madeinchaos/eins2440/hardware/images/1.jpg

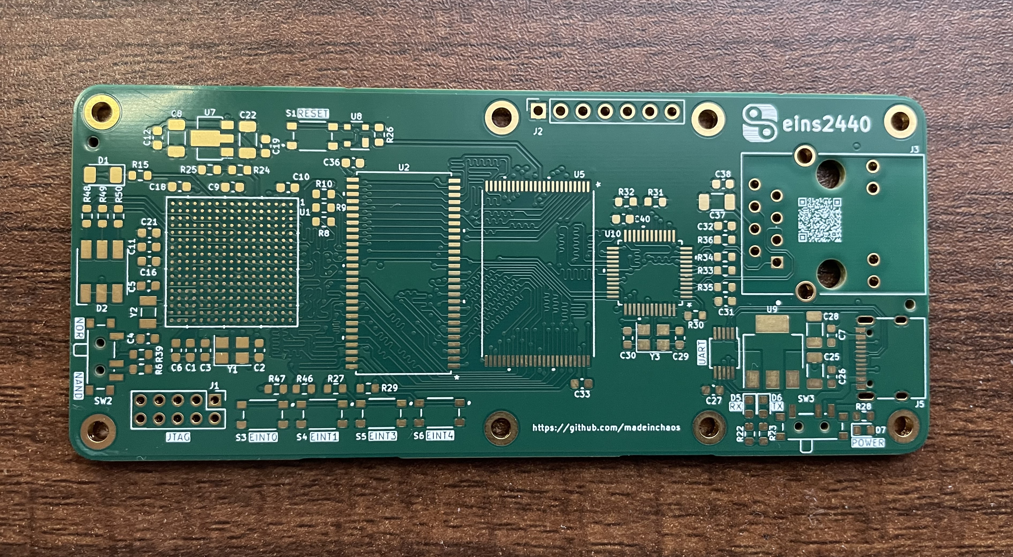
hardware/images/1.jpg
