madeinchaos/eins2440/hardware/images/2.jpg

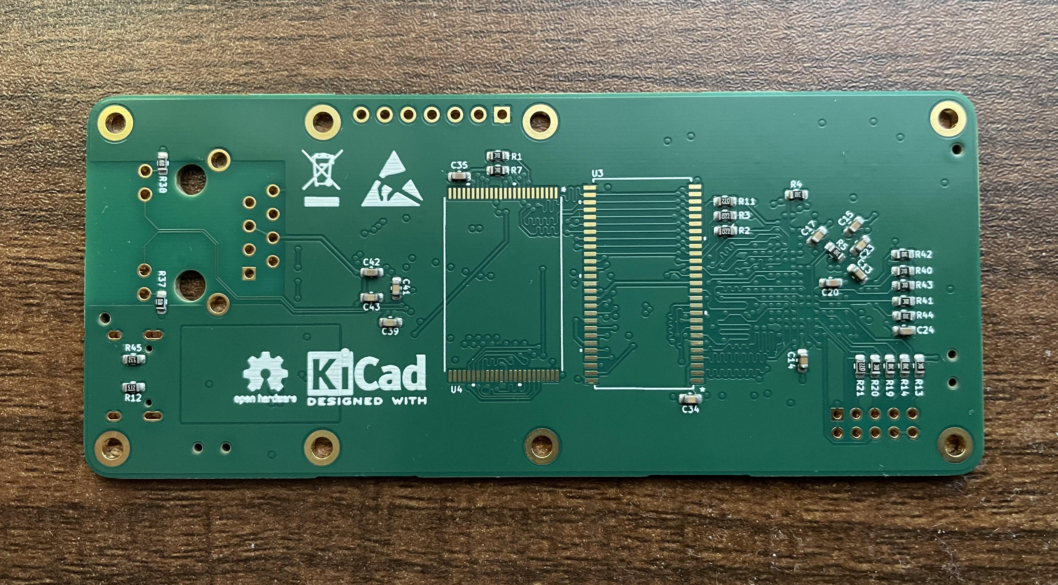
hardware/images/2.jpg
