madeinchaos/eins2440/hardware/images/3.jpg

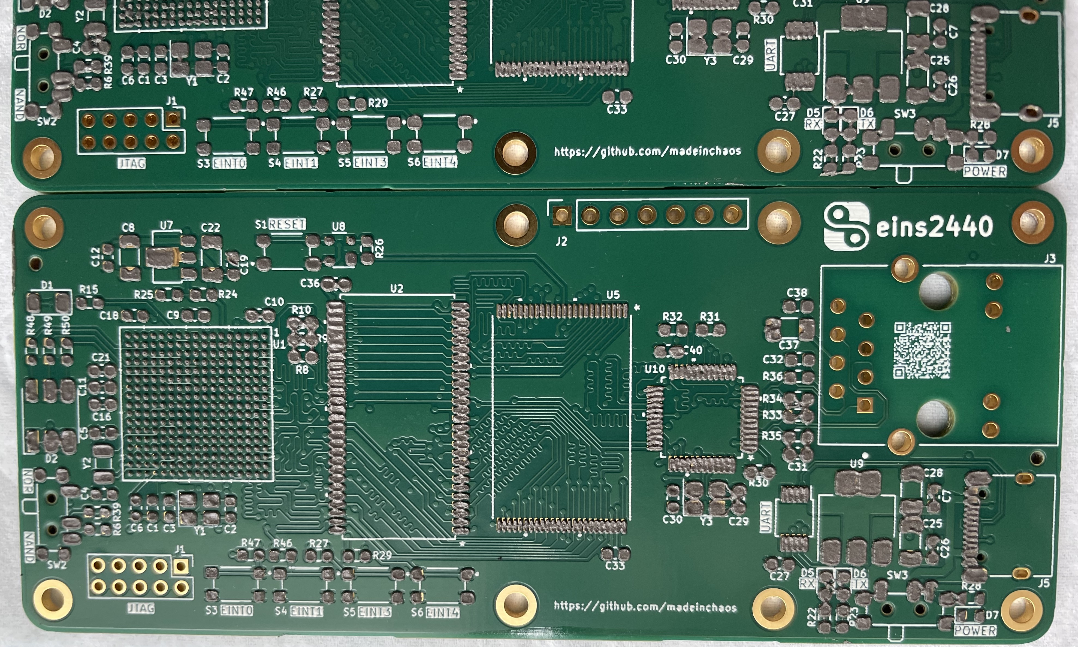
hardware/images/3.jpg
