madeinchaos/eins2440/hardware/images/4.jpg

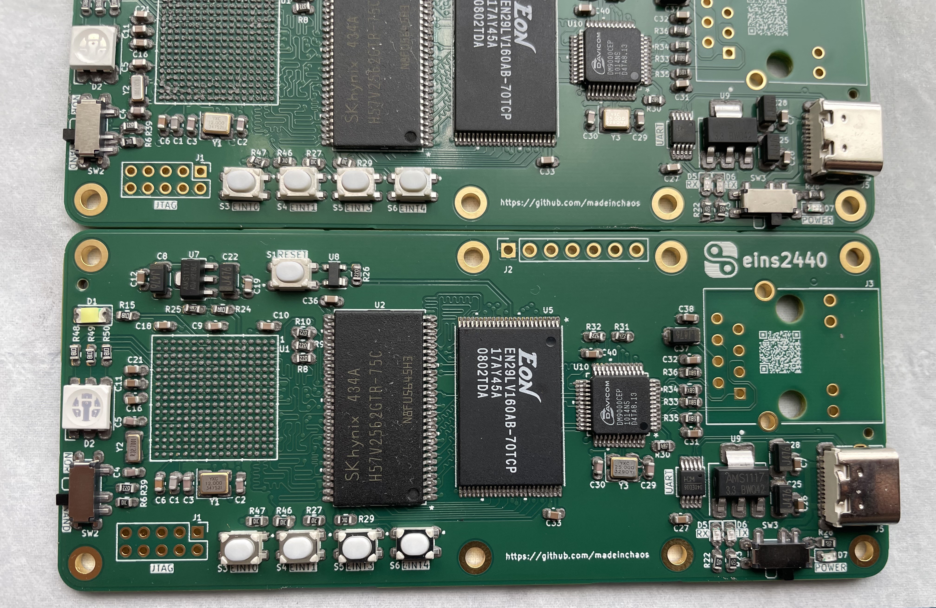
hardware/images/4.jpg
