madeinchaos/eins2440/hardware/kicad/eins2440/ethernet.kicad_sch

## KiCad design hardware/kicad/eins2440/ethernet.kicad_sch (2024-04-18)

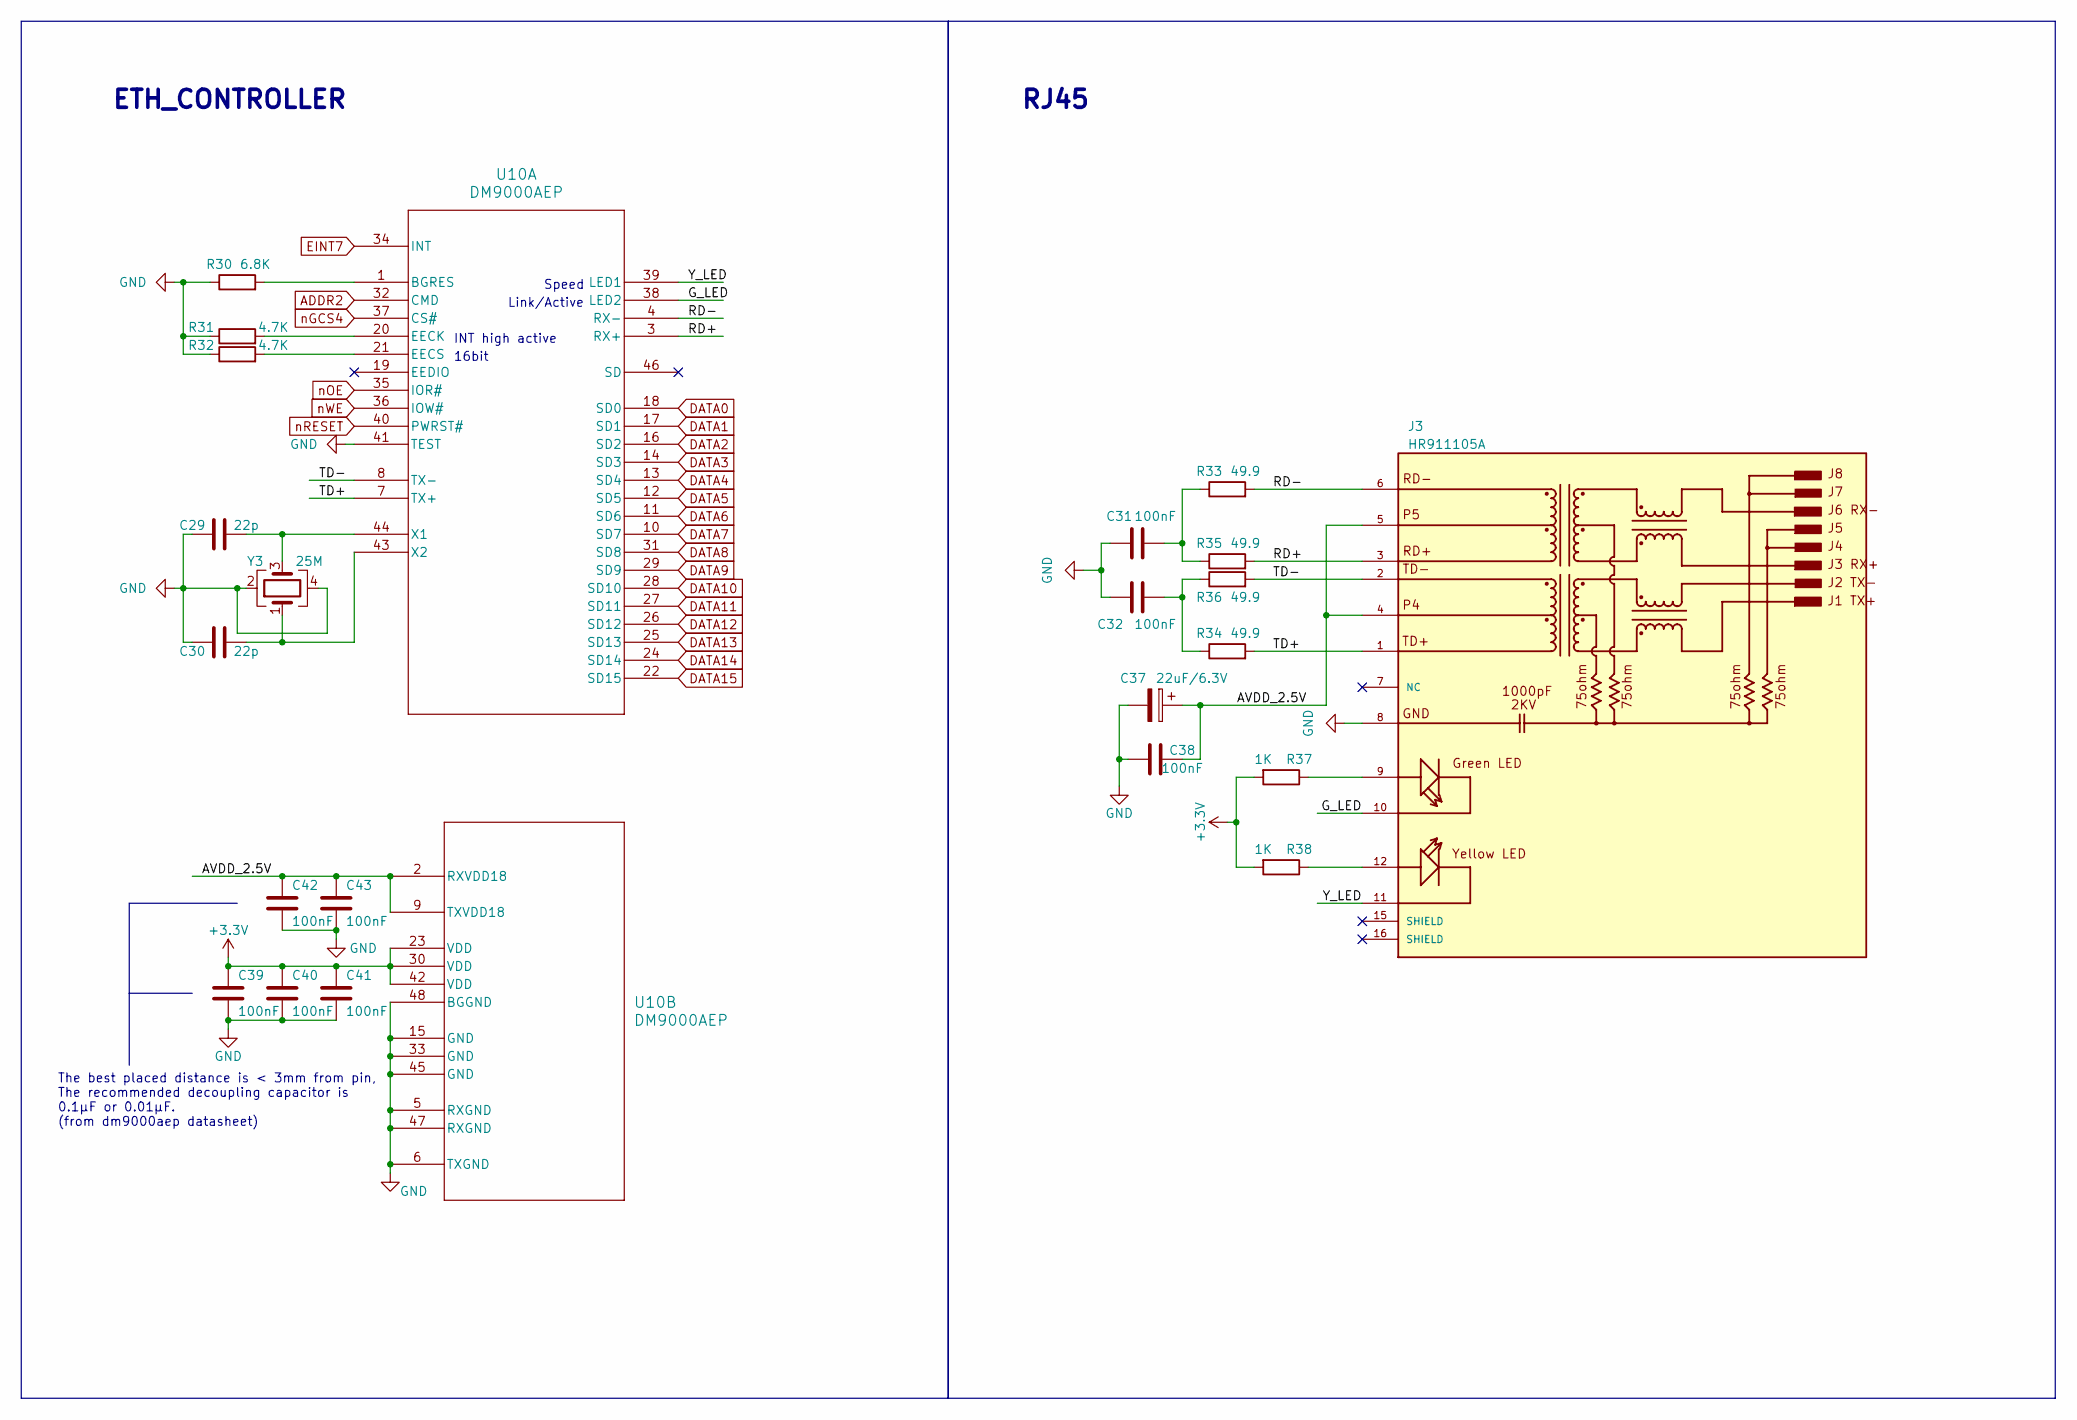
[picture p20: schematic ethernet.kicad_sch]

Parts:
C29, C30: 22p; C_0603_1608Metric
C31, C32, C38, C39, C40, C41, C42, C43: 100nF; C_0603_1608Metric
C37: 22uF/6.3V; C_1206_3216Metric
J3: HR911105A; HANRUN_HR911105A; PARTREV A
R30: 6.8K; R_0603_1608Metric
R31, R32: 4.7K; R_0603_1608Metric
R33, R34, R35, R36: 49.9; R_0603_1608Metric
R37, R38: 1K; R_0603_1608Metric
U10: DM9000AEP; QFP_9000BEP_DAV
Y3: 25M; Crystal_SMD_3225-4Pin_3.2x2.5mm

Connections:
+3.3V: C39.1, C40.1, C41.1, R37.2, R38.2, U10.23 (VDD), U10.30 (VDD), U10.42 (VDD)
ADDR2: U10.32 (CMD)
AVDD_2.5V: C37.1, C38.2, C42.1, C43.1, J3.4, J3.5, U10.2 (RXVDD18), U10.9 (TXVDD18)
DATA0: U10.18 (SD0)
DATA1: U10.17 (SD1)
DATA2: U10.16 (SD2)
DATA3: U10.14 (SD3)
DATA4: U10.13 (SD4)
DATA5: U10.12 (SD5)
DATA6: U10.11 (SD6)
DATA7: U10.10 (SD7)
DATA8: U10.31 (SD8)
DATA9: U10.29 (SD9)
DATA10: U10.28 (SD10)
DATA11: U10.27 (SD11)
DATA12: U10.26 (SD12)
DATA13: U10.25 (SD13)
DATA14: U10.24 (SD14)
DATA15: U10.22 (SD15)
EINT7: U10.34 (INT)
GND: C29.1, C30.1, C31.1, C32.1, C37.2, C38.1, C39.2, C40.2, C41.2, C42.2, C43.2, J3.8, R30.1, R31.1, R32.1, U10.5 (RXGND), U10.6 (TXGND), U10.15 (GND), U10.33 (GND), U10.41 (TEST), U10.45 (GND), U10.47 (RXGND), U10.48 (BGGND), Y3.2, Y3.4
G_LED: J3.10, U10.38 (LED2)
unnamed: C29.2, U10.44 (X1), Y3.3
unnamed: C30.2, U10.43 (X2), Y3.1
unnamed: C31.2, R33.1, R35.1
unnamed: C32.2, R34.1, R36.1
unnamed: J3.9, R37.1
unnamed: J3.12, R38.1
unnamed: R30.2, U10.1 (BGRES)
unnamed: R31.2, U10.20 (EECK)
unnamed: R32.2, U10.21 (EECS)
RD+: J3.3, R35.2, U10.3 (RX+)
RD-: J3.6, R33.2, U10.4 (RX-)
TD+: J3.1, R34.2, U10.7 (TX+)
TD-: J3.2, R36.2, U10.8 (TX-)
Y_LED: J3.11, U10.39 (LED1)
nGCS4: U10.37 (CS#)
nOE: U10.35 (IOR#)
nRESET: U10.40 (PWRST#)
nWE: U10.36 (IOW#)

Notes on the sheet:
RJ45
ETH_CONTROLLER
The best placed distance is < 3mm from pin, The recommended decoupling capacitor is 0.1μF or 0.01μF. (from dm9000aep datasheet)
Speed
INT high active
Link/Active
16bit
