madeinchaos/eins2440/hardware/kicad/eins2440/flash.kicad_sch

## KiCad design hardware/kicad/eins2440/flash.kicad_sch (2024-04-18)

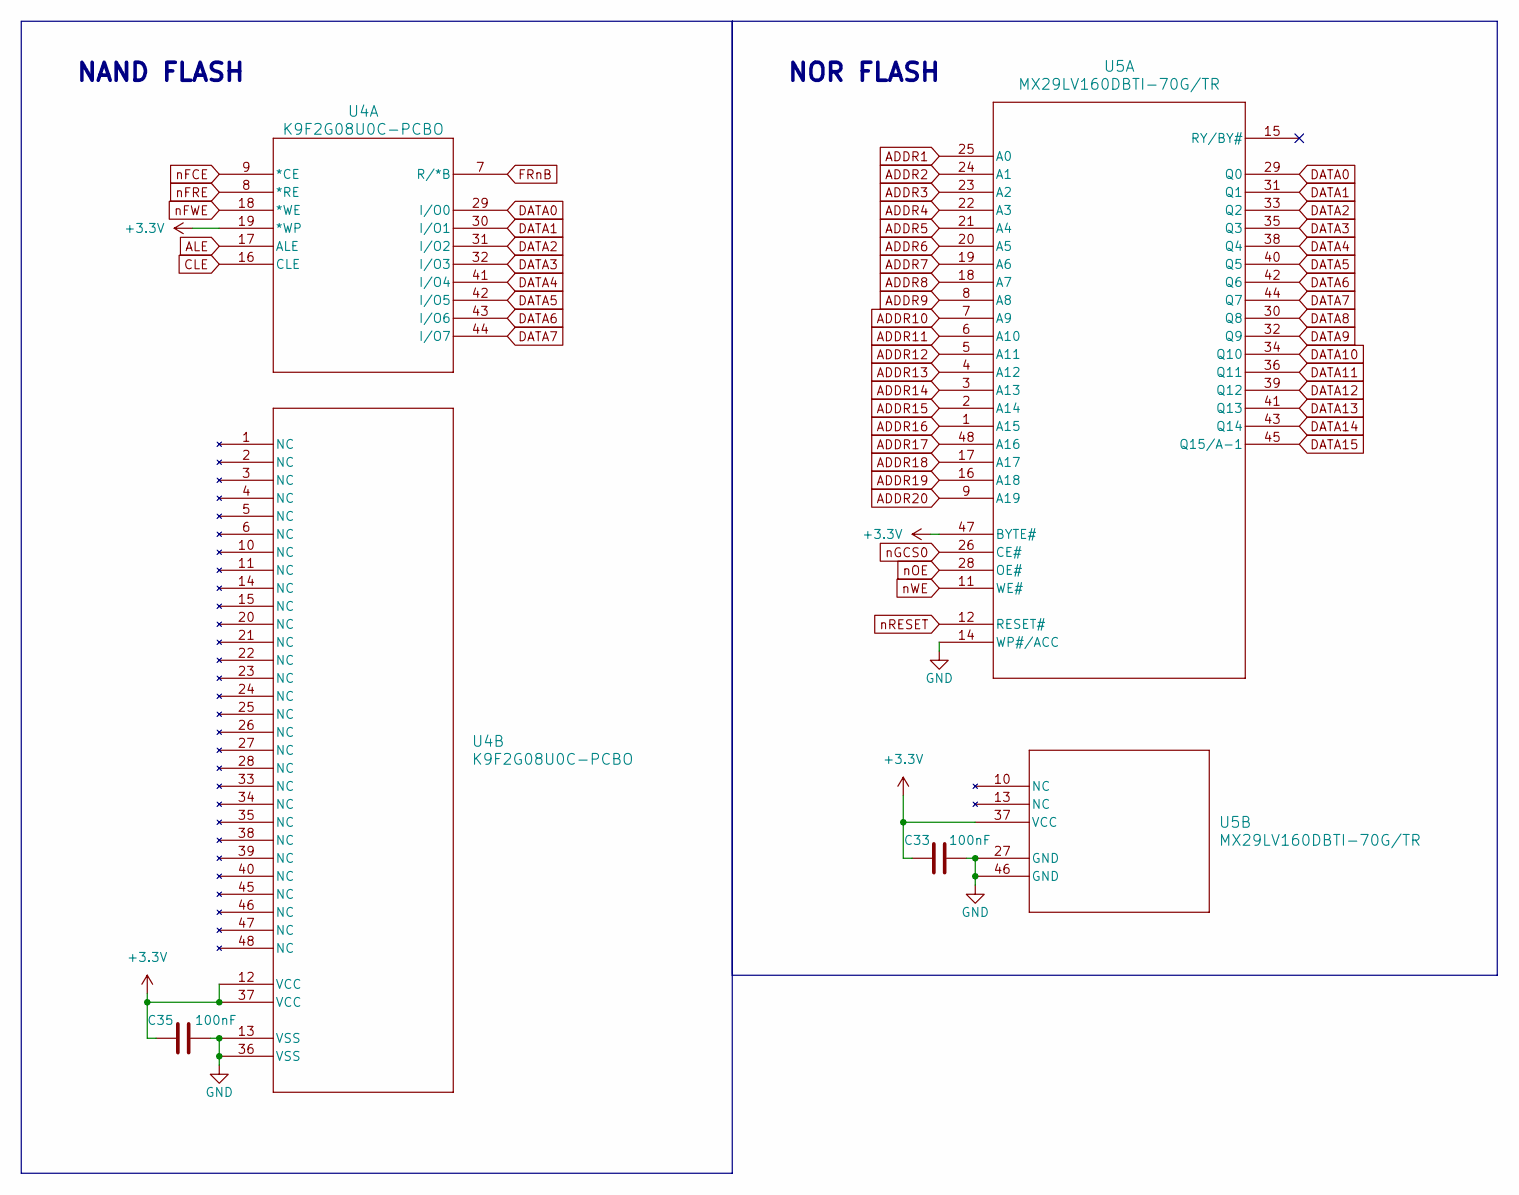
[picture p21: schematic flash.kicad_sch]

Parts:
C33, C35: 100nF; C_0603_1608Metric
U4: K9F2G08U0C-PCBO; TSOP1-48L_SAM
U5: MX29LV160DBTI-70G/TR; TSOP1-48L_SAM

Connections:
+3.3V: C33.2, C35.1, U4.12 (VCC), U4.19 (*WP), U4.37 (VCC), U5.37 (VCC), U5.47 (BYTE#)
ADDR1: U5.25 (A0)
ADDR2: U5.24 (A1)
ADDR3: U5.23 (A2)
ADDR4: U5.22 (A3)
ADDR5: U5.21 (A4)
ADDR6: U5.20 (A5)
ADDR7: U5.19 (A6)
ADDR8: U5.18 (A7)
ADDR9: U5.8 (A8)
ADDR10: U5.7 (A9)
ADDR11: U5.6 (A10)
ADDR12: U5.5 (A11)
ADDR13: U5.4 (A12)
ADDR14: U5.3 (A13)
ADDR15: U5.2 (A14)
ADDR16: U5.1 (A15)
ADDR17: U5.48 (A16)
ADDR18: U5.17 (A17)
ADDR19: U5.16 (A18)
ADDR20: U5.9 (A19)
ALE: U4.17 (ALE)
CLE: U4.16 (CLE)
DATA0: U4.29 (I/O0), U5.29 (Q0)
DATA1: U4.30 (I/O1), U5.31 (Q1)
DATA2: U4.31 (I/O2), U5.33 (Q2)
DATA3: U4.32 (I/O3), U5.35 (Q3)
DATA4: U4.41 (I/O4), U5.38 (Q4)
DATA5: U4.42 (I/O5), U5.40 (Q5)
DATA6: U4.43 (I/O6), U5.42 (Q6)
DATA7: U4.44 (I/O7), U5.44 (Q7)
DATA8: U5.30 (Q8)
DATA9: U5.32 (Q9)
DATA10: U5.34 (Q10)
DATA11: U5.36 (Q11)
DATA12: U5.39 (Q12)
DATA13: U5.41 (Q13)
DATA14: U5.43 (Q14)
DATA15: U5.45 (Q15/A-1)
FRnB: U4.7 (R/*B)
GND: C33.1, C35.2, U4.13 (VSS), U4.36 (VSS), U5.14 (WP#/ACC), U5.27 (GND), U5.46 (GND)
nFCE: U4.9 (*CE)
nFRE: U4.8 (*RE)
nFWE: U4.18 (*WE)
nGCS0: U5.26 (CE#)
nOE: U5.28 (OE#)
nRESET: U5.12 (RESET#)
nWE: U5.11 (WE#)

Notes on the sheet:
NOR FLASH
NAND FLASH
