madeinchaos/eins2440/hardware/kicad/eins2440/misc.kicad_sch

## KiCad design hardware/kicad/eins2440/misc.kicad_sch (2024-04-18)

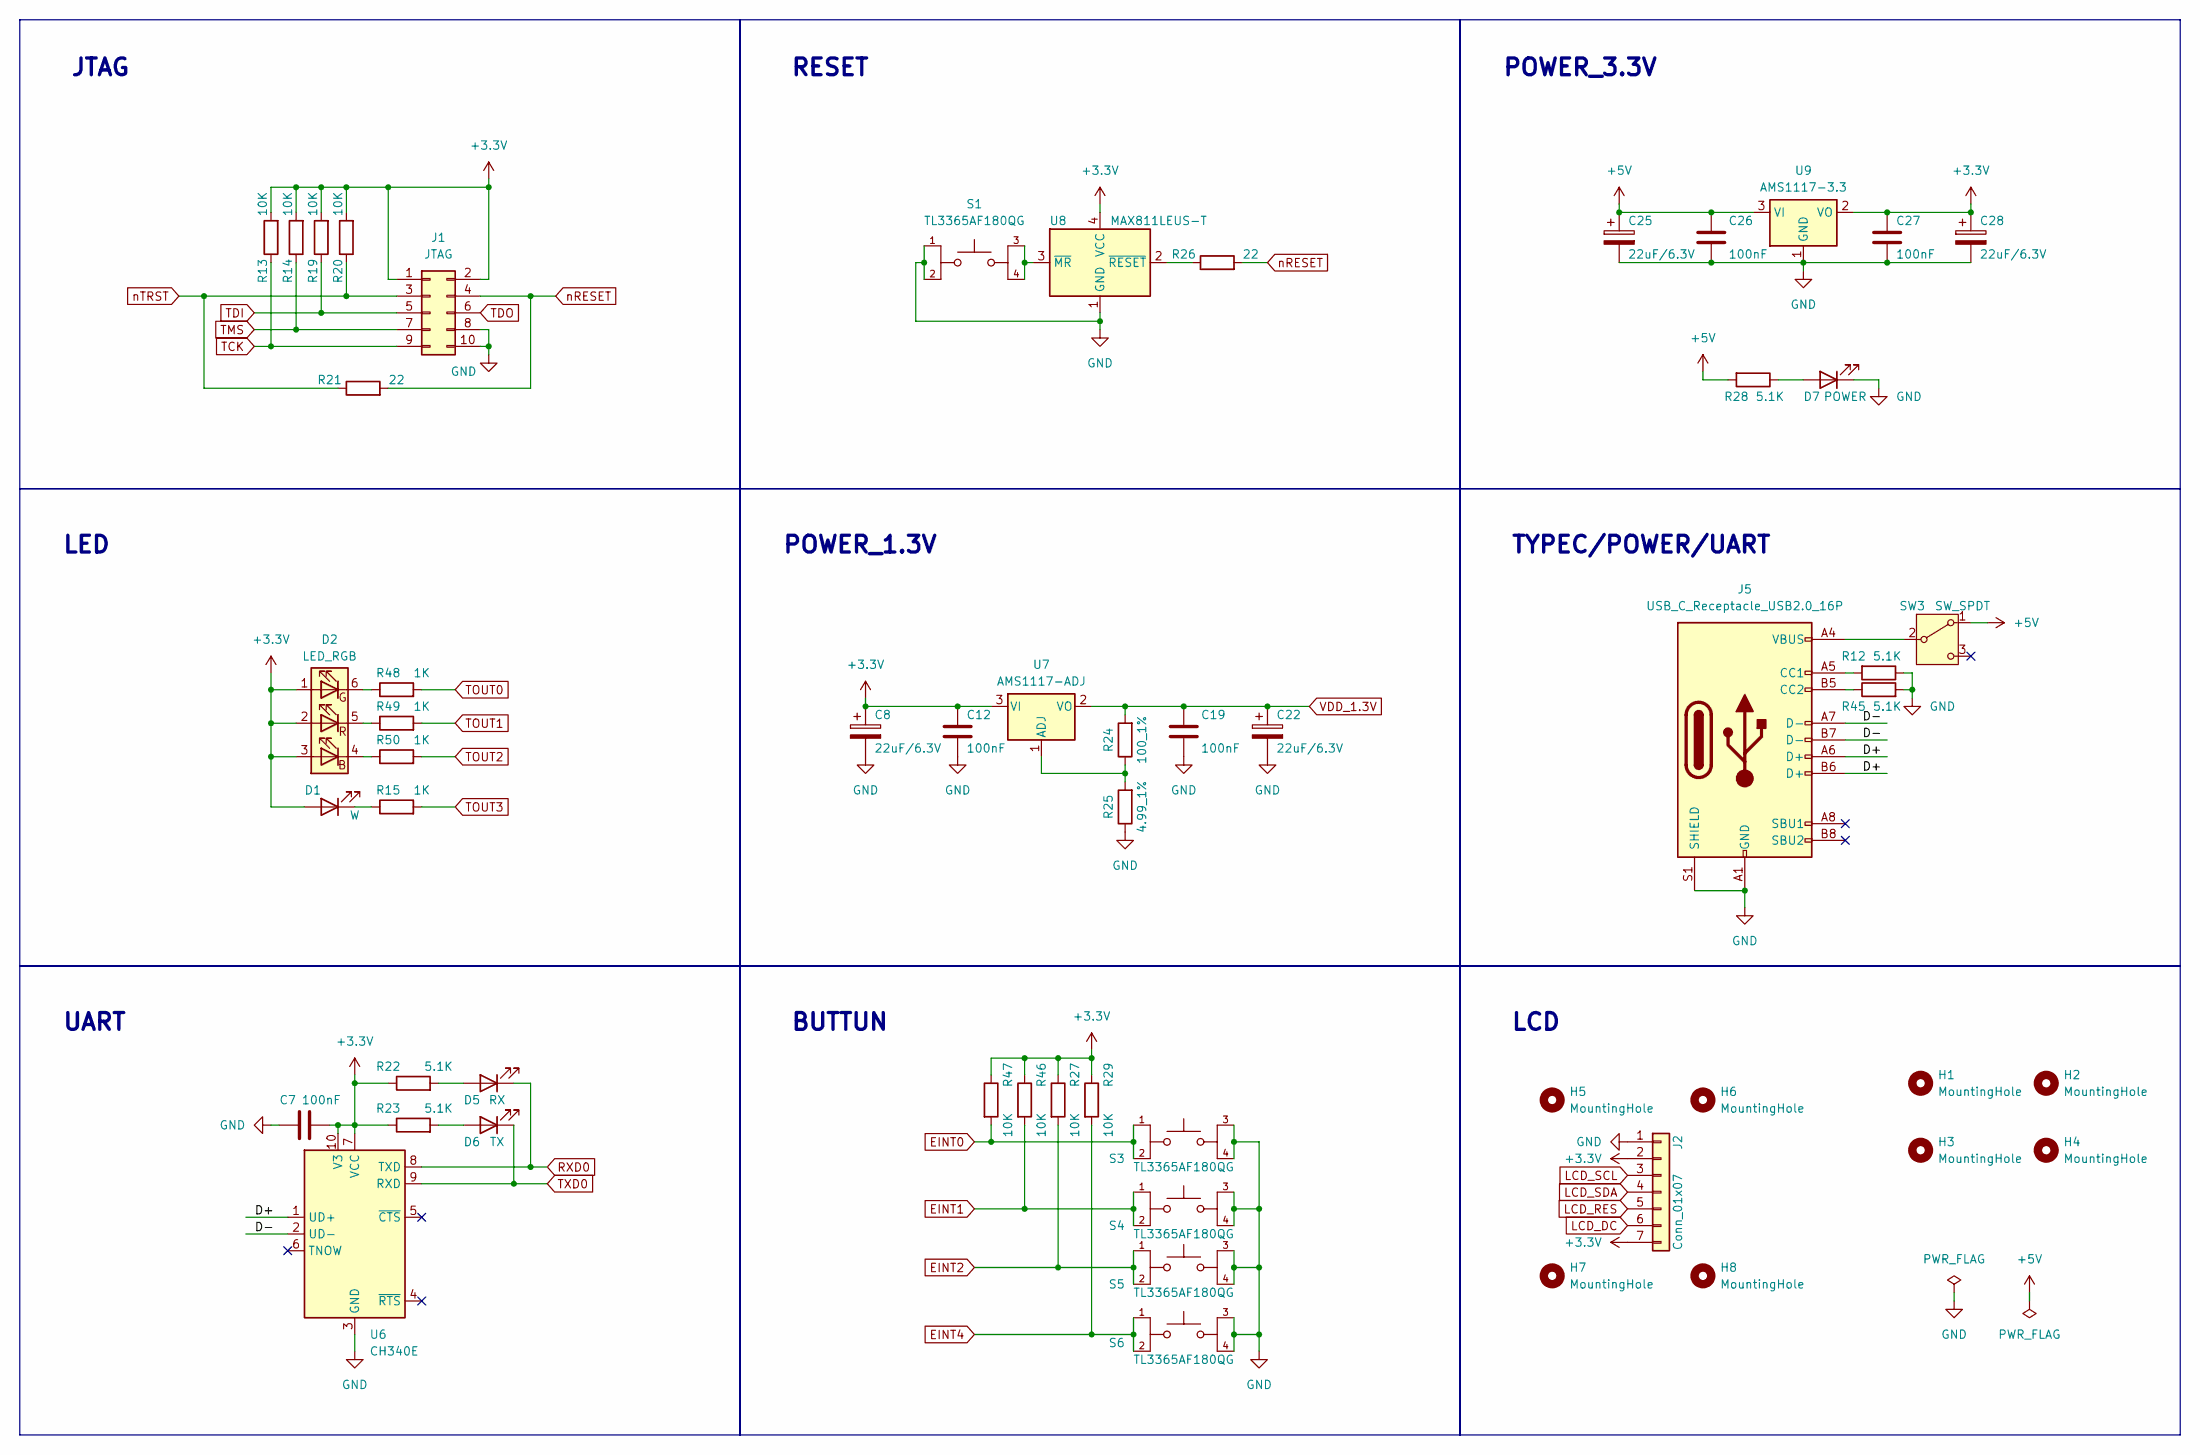
[picture p22: schematic misc.kicad_sch]

Parts:
C7, C12, C19, C26, C27: 100nF; C_0603_1608Metric
C8, C22, C25, C28: 22uF/6.3V; C_1206_3216Metric
D1: W; LED_1206_3216Metric
D2: LED_RGB; LED_RGB_5050-6
D5: RX; LED_0603_1608Metric
D6: TX; LED_0603_1608Metric
D7: POWER; LED_0603_1608Metric
H1, H2, H3, H4, H5, H6, H7, H8: MountingHole; MountingHole_2.2mm_M2_DIN965_Pad
J1: JTAG; PinHeader_2x05_P2.00mm_Vertical
J2: Conn_01x07; PinSocket_1x07_P2.54mm_Vertical
J5: USB_C_Receptacle_USB2.0_16P; USB_C_Receptacle_XKB_U262-16XN-4BVC11
R12, R22, R23, R28, R45: 5.1K; R_0603_1608Metric
R13, R14, R19, R20, R27, R29, R46, R47: 10K; R_0603_1608Metric
R15, R48, R49, R50: 1K; R_0603_1608Metric
R21, R26: 22; R_0603_1608Metric
R24: 100_1%; R_0603_1608Metric
R25: 4.99_1%; R_0603_1608Metric
S1, S3, S4, S5, S6: TL3365AF180QG; SW_TL3365AF180QG; PARTREV A
SW3: SW_SPDT; SW_SPDT_PCM12
U6: CH340E; MSOP-10_3x3mm_P0.5mm
U7: AMS1117-ADJ; SOT-89-3
U8: MAX811LEUS-T; SOT-143
U9: AMS1117-3.3; SOT-223-3_TabPin2

Connections:
+3.3V: C7.1, C8.1, C12.1, C27.1, C28.1, D1.2 (A), D2.1 (GA), D2.2 (RA), D2.3 (BA), J1.1, J1.2, J2.2, J2.7, R13.2, R14.2, R19.2, R20.2, R22.1, R23.1, R27.1, R29.1, R46.1, R47.1, U6.7 (VCC), U6.10 (V3), U7.3 (VI), U8.4 (VCC), U9.2 (VO)
+5V: C25.1, C26.1, R28.2, SW3.1 (A), U9.3 (VI)
D+: J5.A6 (D+), J5.B6 (D+), U6.1 (UD+)
D-: J5.A7 (D-), J5.B7 (D-), U6.2 (UD-)
EINT0: R47.2, S3.1, S3.2
EINT1: R46.2, S4.1, S4.2
EINT2: R27.2, S5.1, S5.2
EINT4: R29.2, S6.1, S6.2
GND: C7.2, C8.2, C12.2, C19.2, C22.2, C25.2, C26.2, C27.2, C28.2, D7.1 (K), J1.8, J1.10, J2.1, J5.A1 (GND), J5.A12 (GND), J5.B1 (GND), J5.B12 (GND), J5.S1 (SHIELD), R12.1, R25.1, R45.2, S1.1, S1.2, S3.3, S3.4, S4.3, S4.4, S5.3, S5.4, S6.3, S6.4, U6.3 (GND), U8.1 (GND), U9.1 (GND)
LCD_DC: J2.6
LCD_RES: J2.5
LCD_SCL: J2.3
LCD_SDA: J2.4
unnamed: D1.1 (K), R15.1
unnamed: D2.4 (BK), R50.1
unnamed: D2.5 (RK), R49.1
unnamed: D2.6 (GK), R48.1
unnamed: D5.2 (A), R22.2
unnamed: D6.2 (A), R23.2
unnamed: D7.2 (A), R28.1
unnamed: J5.A4 (VBUS), J5.A9 (VBUS), J5.B4 (VBUS), J5.B9 (VBUS), SW3.2 (B)
unnamed: J5.A5 (CC1), R12.2
unnamed: J5.B5 (CC2), R45.1
unnamed: R24.1, R25.2, U7.1 (ADJ)
unnamed: R26.1, U8.2 (~RESET)
unnamed: S1.3, S1.4, U8.3 (~MR)
RXD0: D5.1 (K), U6.8 (TXD)
TCK: J1.9, R13.1
TDI: J1.5, R19.1
TDO: J1.6
TMS: J1.7, R14.1
TOUT0: R48.2
TOUT1: R49.2
TOUT2: R50.2
TOUT3: R15.2
TXD0: D6.1 (K), U6.9 (RXD)
VDD_1.3V: C19.1, C22.1, R24.2, U7.2 (VO)
nRESET: J1.4, R21.2, R26.2
nTRST: J1.3, R20.1, R21.1

Notes on the sheet:
TYPEC/POWER/UART
POWER_3.3V
POWER_1.3V
BUTTUN
LED
UART
RESET
LCD
JTAG
