madeinchaos/eins2440/hardware/kicad/eins2440/power.kicad_sch

## KiCad design hardware/kicad/eins2440/power.kicad_sch (2024-04-18)

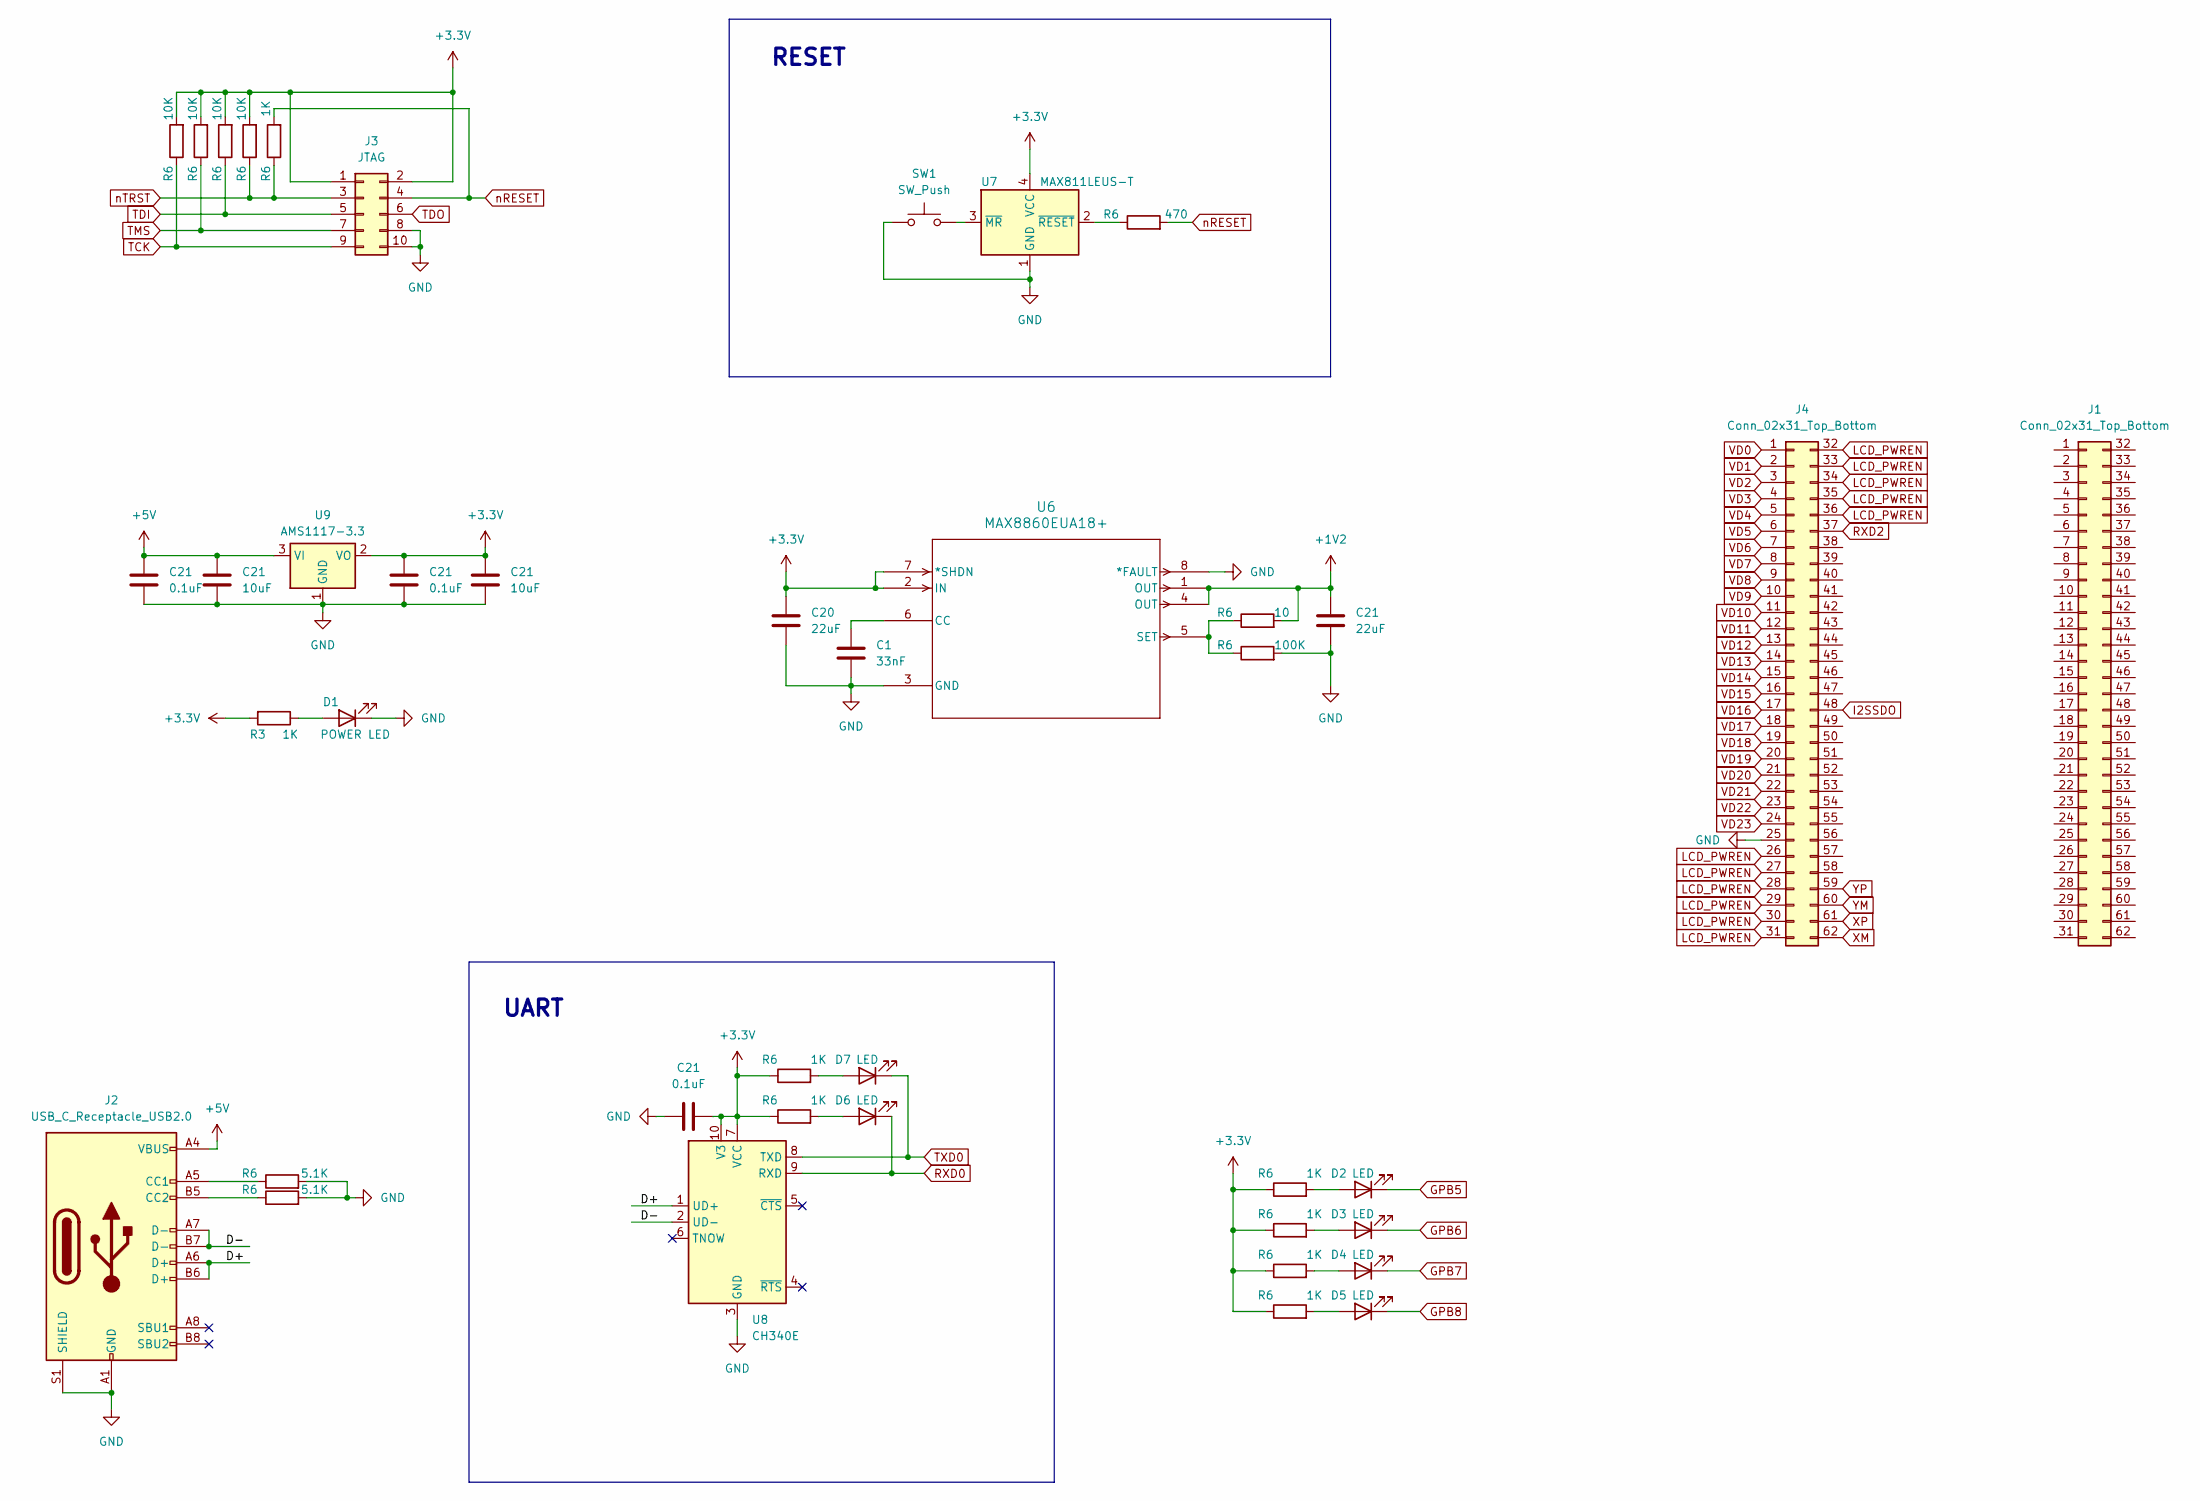
[picture p23: schematic power.kicad_sch]

Parts:
C1: 33nF; C_0603_1608Metric
C20: 22uF; C_0603_1608Metric
C21: 10uF; C_0603_1608Metric
D1: POWER LED; LED_0603_1608Metric
D2, D3, D4, D5, D6, D7: LED; LED_0603_1608Metric
J1, J4: Conn_02x31_Top_Bottom
J2: USB_C_Receptacle_USB2.0; USB_C_Receptacle_XKB_U262-16XN-4BVC11
J3: JTAG
R3: 1K; R_0603_1608Metric
R6: 10; R_0603_1608Metric
SW1: SW_Push; SW_SPST_TL3305A
U6: MAX8860EUA18+
U7: MAX811LEUS-T; SOT-143
U8: CH340E; MSOP-10_3x3mm_P0.5mm
U9: AMS1117-3.3; SOT-223-3_TabPin2

Connections:
+1V2: C21.2, R6.2, U6.1 (OUT), U6.4 (OUT)
+3.3V: C20.1, C21.1, J3.1, J3.2, R3.2, R6.1, R6.2, U6.2 (IN), U6.7 (*SHDN), U7.4 (VCC), U8.7 (VCC), U8.10 (V3), U9.2 (VO)
+5V: C21.1, C21.2, J2.A4 (VBUS), J2.A9 (VBUS), J2.B4 (VBUS), J2.B9 (VBUS), U9.3 (VI)
D+: J2.A6 (D+), J2.B6 (D+), U8.1 (UD+)
D-: J2.A7 (D-), J2.B7 (D-), U8.2 (UD-)
GND: C1.2, C20.2, C21.1, C21.2, D1.1 (K), J2.A1 (GND), J2.A12 (GND), J2.B1 (GND), J2.B12 (GND), J2.S1 (SHIELD), J3.8, J3.10, J4.25, R6.2, SW1.1, U6.3 (GND), U6.8 (*FAULT), U7.1 (GND), U8.3 (GND), U9.1 (GND)
GPB5: D2.1 (K)
GPB6: D3.1 (K)
GPB7: D4.1 (K)
GPB8: D5.1 (K)
I2SSDO: J4.48
LCD_PWREN: J4.26, J4.27, J4.28, J4.29, J4.30, J4.31, J4.32, J4.33, J4.34, J4.35, J4.36
unnamed: C1.1, U6.6 (CC)
unnamed: D1.2 (A), R3.1
unnamed: D2.2 (A), R6.2
unnamed: D3.2 (A), R6.2
unnamed: D4.2 (A), R6.2
unnamed: D5.2 (A), R6.2
unnamed: D6.2 (A), R6.2
unnamed: D7.2 (A), R6.2
unnamed: J2.A5 (CC1), R6.1
unnamed: J2.B5 (CC2), R6.1
unnamed: R6.1, U6.5 (SET), U7.2 (~RESET)
unnamed: SW1.2, U7.3 (~MR)
RXD0: D6.1 (K), U8.9 (RXD)
RXD2: J4.37
TCK: J3.9, R6.1
TDI: J3.5, R6.1
TDO: J3.6
TMS: J3.7, R6.1
TXD0: D7.1 (K), U8.8 (TXD)
VD0: J4.1
VD1: J4.2
VD2: J4.3
VD3: J4.4
VD4: J4.5
VD5: J4.6
VD6: J4.7
VD7: J4.8
VD8: J4.9
VD9: J4.10
VD10: J4.11
VD11: J4.12
VD12: J4.13
VD13: J4.14
VD14: J4.15
VD15: J4.16
VD16: J4.17
VD17: J4.18
VD18: J4.19
VD19: J4.20
VD20: J4.21
VD21: J4.22
VD22: J4.23
VD23: J4.24
XM: J4.62
XP: J4.61
YM: J4.60
YP: J4.59
nRESET: J3.4, R6.2
nTRST: J3.3, R6.1

Notes on the sheet:
UART
RESET
