madeinchaos/eins2440/hardware/kicad/eins2440/ram.kicad_sch

## KiCad design hardware/kicad/eins2440/ram.kicad_sch (2024-04-18)

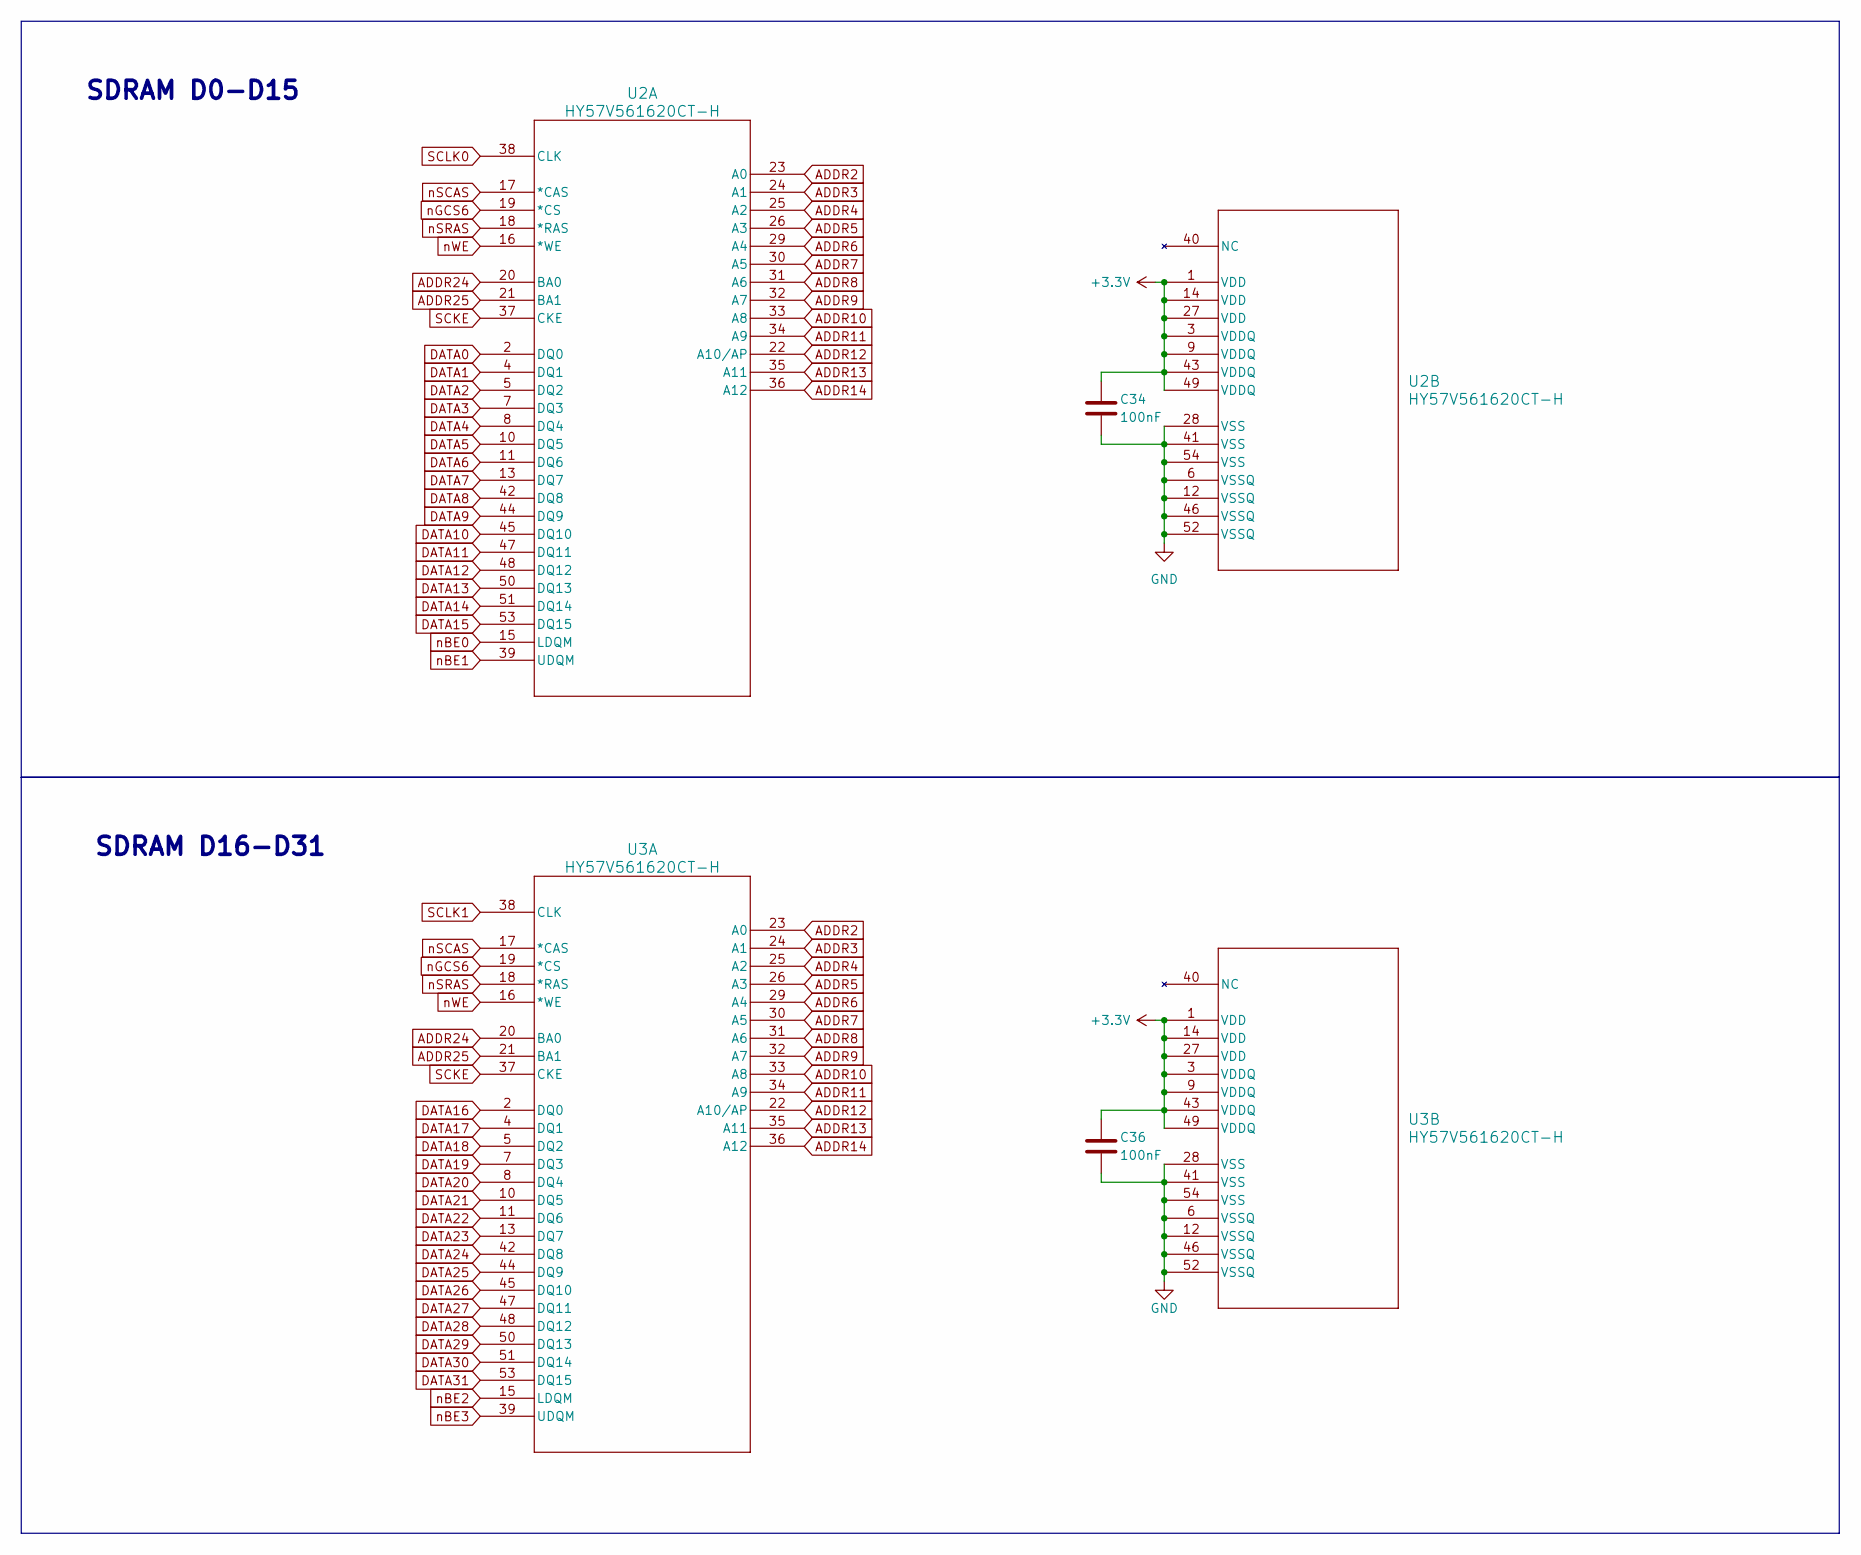
[picture p24: schematic ram.kicad_sch]

Parts:
C34, C36: 100nF; C_0603_1608Metric
U2, U3: HY57V561620CT-H; TSOP54_HNX

Connections:
+3.3V: C34.1, C36.1, U2.1 (VDD), U2.3 (VDDQ), U2.9 (VDDQ), U2.14 (VDD), U2.27 (VDD), U2.43 (VDDQ), U2.49 (VDDQ), U3.1 (VDD), U3.3 (VDDQ), U3.9 (VDDQ), U3.14 (VDD), U3.27 (VDD), U3.43 (VDDQ), U3.49 (VDDQ)
ADDR2: U2.23 (A0), U3.23 (A0)
ADDR3: U2.24 (A1), U3.24 (A1)
ADDR4: U2.25 (A2), U3.25 (A2)
ADDR5: U2.26 (A3), U3.26 (A3)
ADDR6: U2.29 (A4), U3.29 (A4)
ADDR7: U2.30 (A5), U3.30 (A5)
ADDR8: U2.31 (A6), U3.31 (A6)
ADDR9: U2.32 (A7), U3.32 (A7)
ADDR10: U2.33 (A8), U3.33 (A8)
ADDR11: U2.34 (A9), U3.34 (A9)
ADDR12: U2.22 (A10/AP), U3.22 (A10/AP)
ADDR13: U2.35 (A11), U3.35 (A11)
ADDR14: U2.36 (A12), U3.36 (A12)
ADDR24: U2.20 (BA0), U3.20 (BA0)
ADDR25: U2.21 (BA1), U3.21 (BA1)
DATA0: U2.2 (DQ0)
DATA1: U2.4 (DQ1)
DATA2: U2.5 (DQ2)
DATA3: U2.7 (DQ3)
DATA4: U2.8 (DQ4)
DATA5: U2.10 (DQ5)
DATA6: U2.11 (DQ6)
DATA7: U2.13 (DQ7)
DATA8: U2.42 (DQ8)
DATA9: U2.44 (DQ9)
DATA10: U2.45 (DQ10)
DATA11: U2.47 (DQ11)
DATA12: U2.48 (DQ12)
DATA13: U2.50 (DQ13)
DATA14: U2.51 (DQ14)
DATA15: U2.53 (DQ15)
DATA16: U3.2 (DQ0)
DATA17: U3.4 (DQ1)
DATA18: U3.5 (DQ2)
DATA19: U3.7 (DQ3)
DATA20: U3.8 (DQ4)
DATA21: U3.10 (DQ5)
DATA22: U3.11 (DQ6)
DATA23: U3.13 (DQ7)
DATA24: U3.42 (DQ8)
DATA25: U3.44 (DQ9)
DATA26: U3.45 (DQ10)
DATA27: U3.47 (DQ11)
DATA28: U3.48 (DQ12)
DATA29: U3.50 (DQ13)
DATA30: U3.51 (DQ14)
DATA31: U3.53 (DQ15)
GND: C34.2, C36.2, U2.6 (VSSQ), U2.12 (VSSQ), U2.28 (VSS), U2.41 (VSS), U2.46 (VSSQ), U2.52 (VSSQ), U2.54 (VSS), U3.6 (VSSQ), U3.12 (VSSQ), U3.28 (VSS), U3.41 (VSS), U3.46 (VSSQ), U3.52 (VSSQ), U3.54 (VSS)
SCKE: U2.37 (CKE), U3.37 (CKE)
SCLK0: U2.38 (CLK)
SCLK1: U3.38 (CLK)
nBE0: U2.15 (LDQM)
nBE1: U2.39 (UDQM)
nBE2: U3.15 (LDQM)
nBE3: U3.39 (UDQM)
nGCS6: U2.19 (*CS), U3.19 (*CS)
nSCAS: U2.17 (*CAS), U3.17 (*CAS)
nSRAS: U2.18 (*RAS), U3.18 (*RAS)
nWE: U2.16 (*WE), U3.16 (*WE)

Notes on the sheet:
SDRAM D16-D31
SDRAM D0-D15
