madeinchaos/eins2440/hardware/kicad/eins2440/soc.kicad_sch

## KiCad design hardware/kicad/eins2440/soc.kicad_sch (2024-04-18)

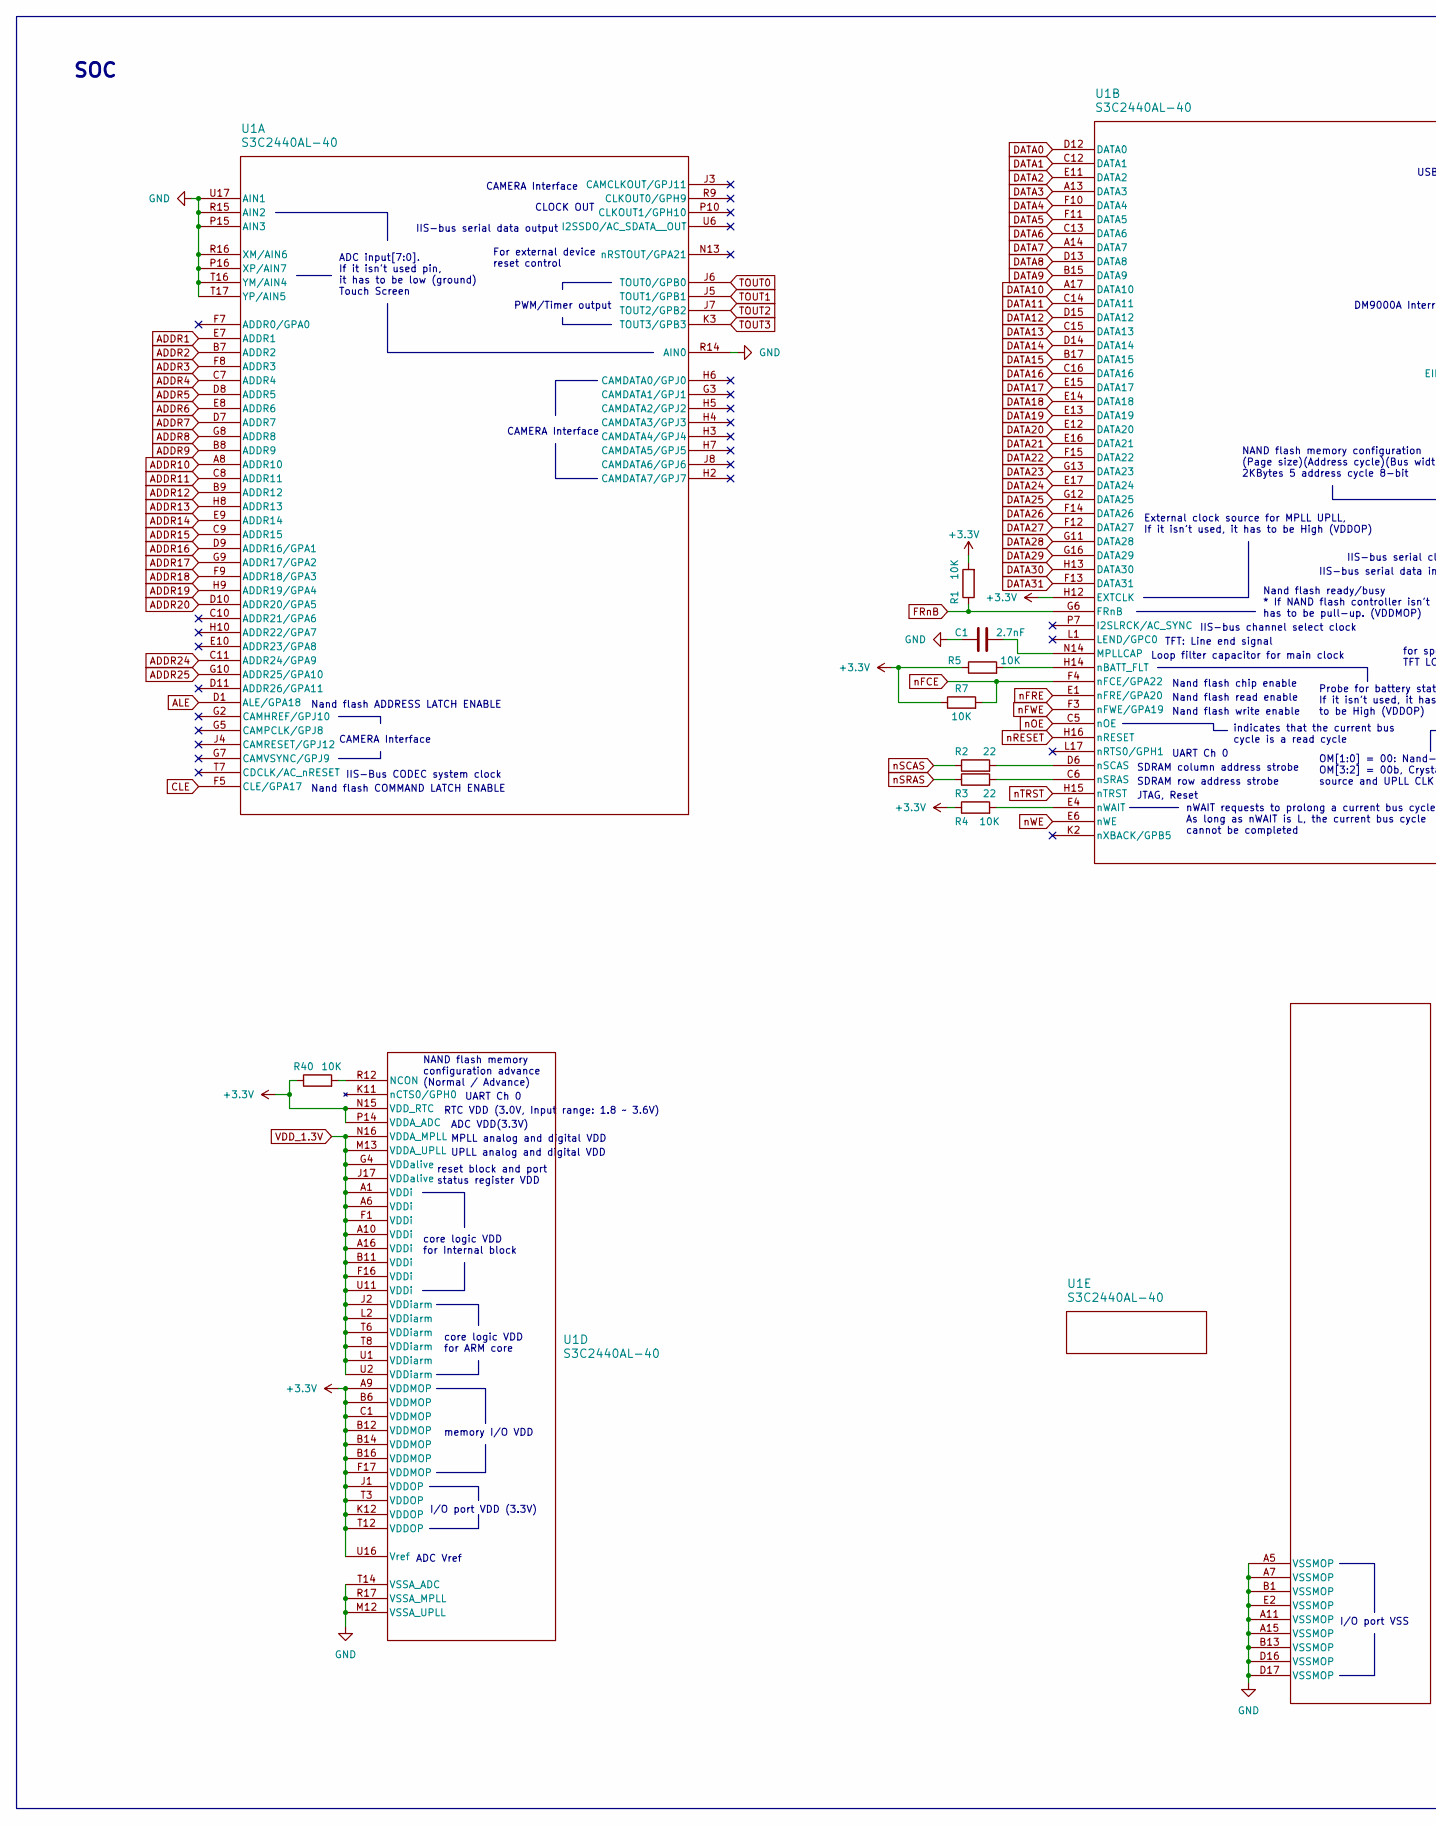
[picture p25: schematic soc.kicad_sch, part in row 1, column 1]

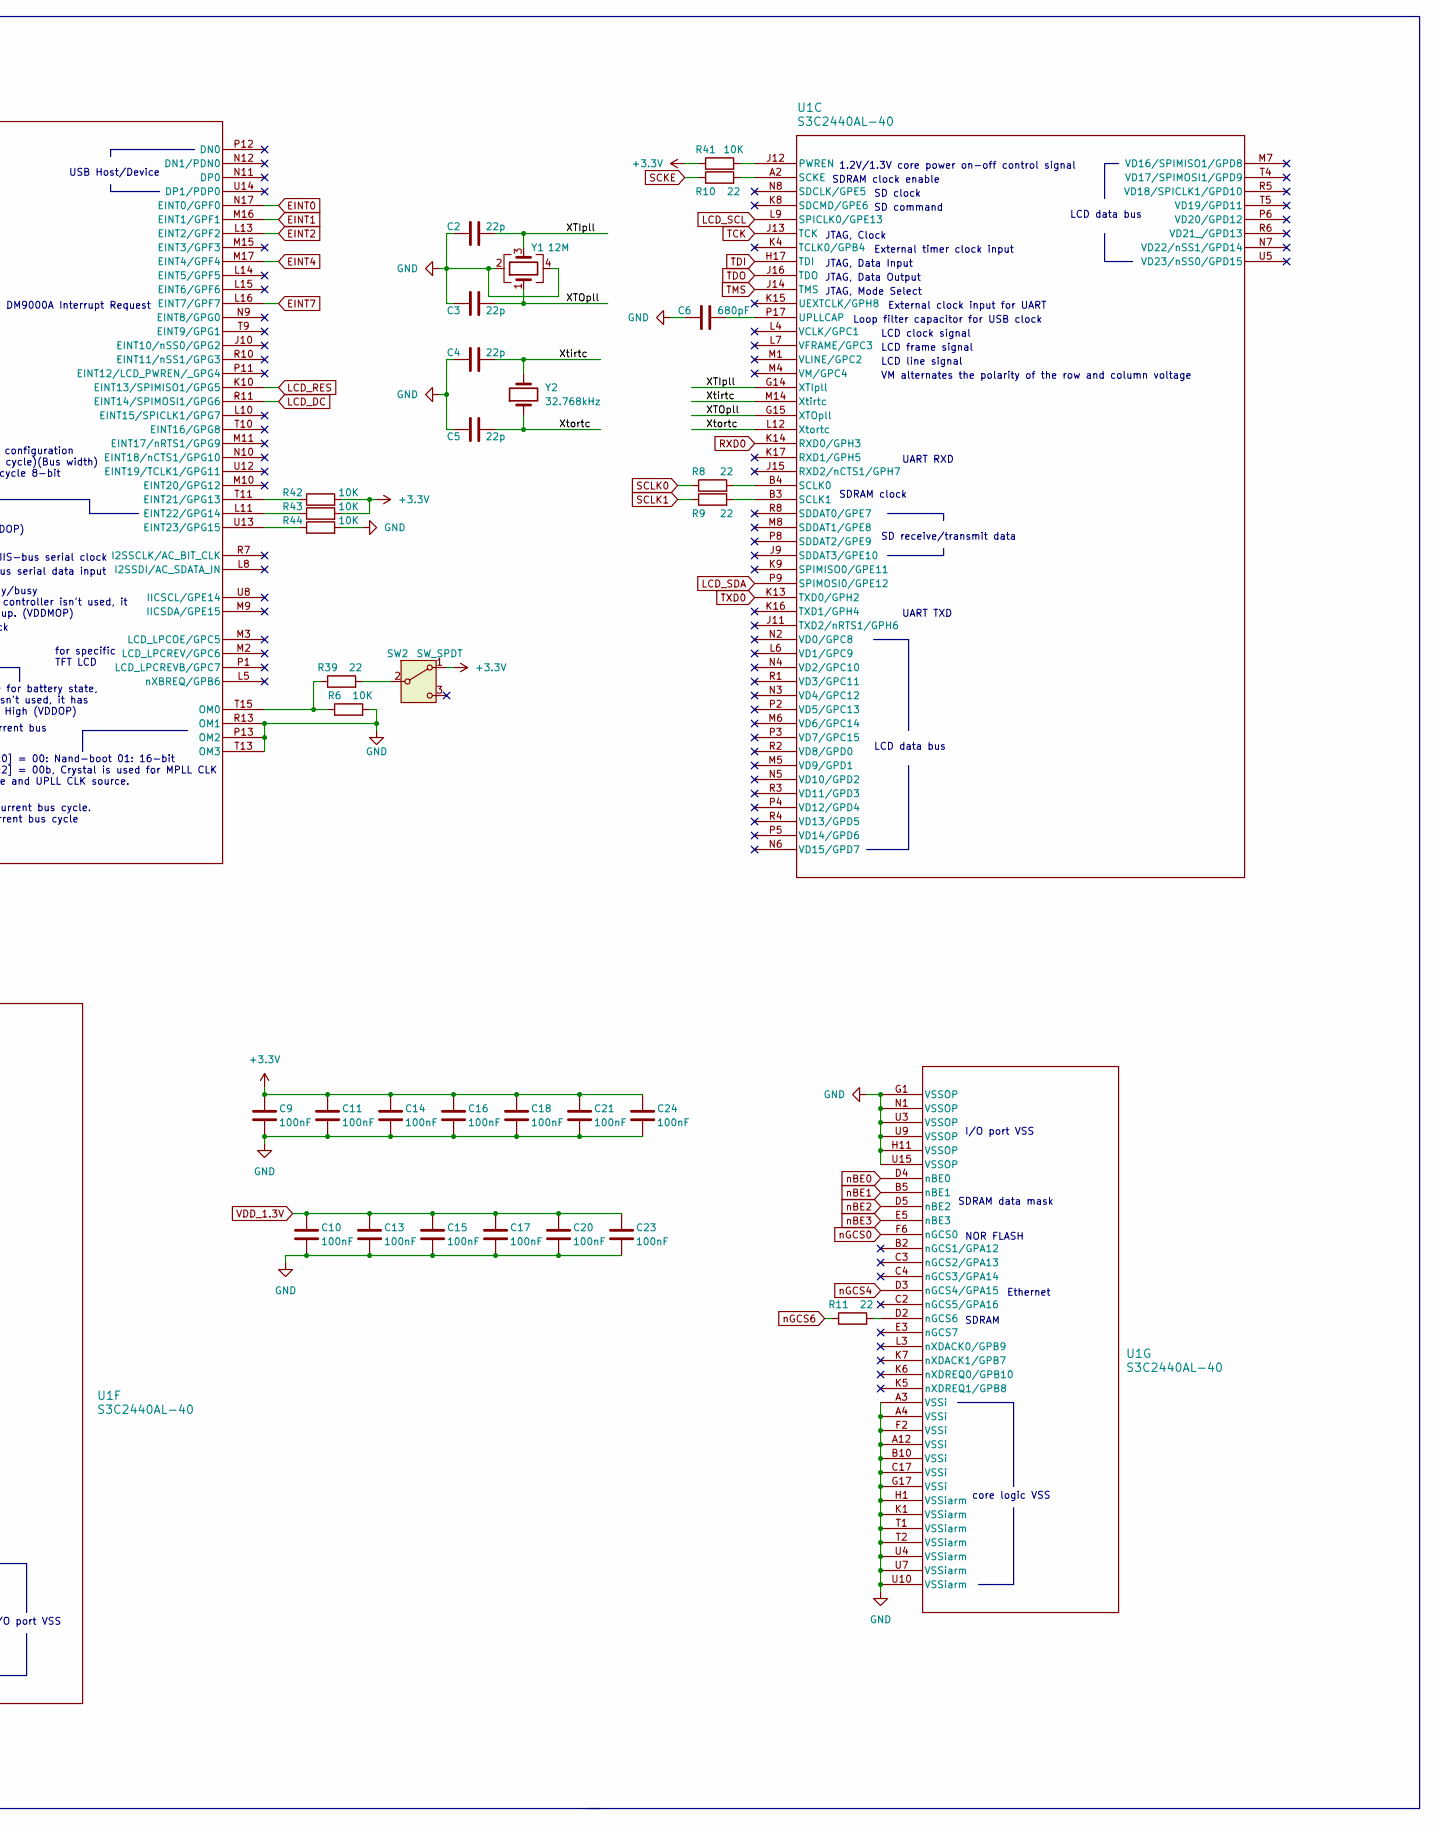
[picture p26: schematic soc.kicad_sch, part in row 1, column 2]

Parts:
C1: 2.7nF; C_0603_1608Metric
C2, C3, C4, C5: 22p; C_0603_1608Metric
C6: 680pF; C_0603_1608Metric
C9, C10, C11, C13, C14, C15, C16, C17, C18, C20, C21, C23, C24: 100nF; C_0603_1608Metric
R1, R4, R5, R6, R7, R40, R41, R42, R43, R44: 10K; R_0603_1608Metric
R2, R3, R8, R9, R10, R11, R39: 22; R_0603_1608Metric
SW2: SW_SPDT; SW_SPDT_PCM12
U1: S3C2440AL-40; S3C2440AL-40_SAM
Y1: 12M; Crystal_SMD_3225-4Pin_3.2x2.5mm
Y2: 32.768kHz; XTAL_CM7V-T1A-32.768KHZ-6PF-10PPM-TA-QC

Connections:
+3.3V: C9.1, C11.1, C14.1, C16.1, C18.1, C21.1, C24.1, R1.2, R4.1, R5.1, R7.1, R40.1, R41.1, R42.2, R43.2, SW2.1 (A), U1.A9 (VDDMOP), U1.B6 (VDDMOP), U1.B12 (VDDMOP), U1.B14 (VDDMOP), U1.B16 (VDDMOP), U1.C1 (VDDMOP), U1.F17 (VDDMOP), U1.H12 (EXTCLK), U1.J1 (VDDOP), U1.K12 (VDDOP), U1.N15 (VDD_RTC), U1.P14 (VDDA_ADC), U1.T3 (VDDOP), U1.T12 (VDDOP), U1.U16 (Vref)
ADDR1: U1.E7 (ADDR1)
ADDR2: U1.B7 (ADDR2)
ADDR3: U1.F8 (ADDR3)
ADDR4: U1.C7 (ADDR4)
ADDR5: U1.D8 (ADDR5)
ADDR6: U1.E8 (ADDR6)
ADDR7: U1.D7 (ADDR7)
ADDR8: U1.G8 (ADDR8)
ADDR9: U1.B8 (ADDR9)
ADDR10: U1.A8 (ADDR10)
ADDR11: U1.C8 (ADDR11)
ADDR12: U1.B9 (ADDR12)
ADDR13: U1.H8 (ADDR13)
ADDR14: U1.E9 (ADDR14)
ADDR15: U1.C9 (ADDR15)
ADDR16: U1.D9 (ADDR16/GPA1)
ADDR17: U1.G9 (ADDR17/GPA2)
ADDR18: U1.F9 (ADDR18/GPA3)
ADDR19: U1.H9 (ADDR19/GPA4)
ADDR20: U1.D10 (ADDR20/GPA5)
ADDR24: U1.C11 (ADDR24/GPA9)
ADDR25: U1.G10 (ADDR25/GPA10)
ALE: U1.D1 (ALE/GPA18)
CLE: U1.F5 (CLE/GPA17)
DATA0: U1.D12 (DATA0)
DATA1: U1.C12 (DATA1)
DATA2: U1.E11 (DATA2)
DATA3: U1.A13 (DATA3)
DATA4: U1.F10 (DATA4)
DATA5: U1.F11 (DATA5)
DATA6: U1.C13 (DATA6)
DATA7: U1.A14 (DATA7)
DATA8: U1.D13 (DATA8)
DATA9: U1.B15 (DATA9)
DATA10: U1.A17 (DATA10)
DATA11: U1.C14 (DATA11)
DATA12: U1.D15 (DATA12)
DATA13: U1.C15 (DATA13)
DATA14: U1.D14 (DATA14)
DATA15: U1.B17 (DATA15)
DATA16: U1.C16 (DATA16)
DATA17: U1.E15 (DATA17)
DATA18: U1.E14 (DATA18)
DATA19: U1.E13 (DATA19)
DATA20: U1.E12 (DATA20)
DATA21: U1.E16 (DATA21)
DATA22: U1.F15 (DATA22)
DATA23: U1.G13 (DATA23)
DATA24: U1.E17 (DATA24)
DATA25: U1.G12 (DATA25)
DATA26: U1.F14 (DATA26)
DATA27: U1.F12 (DATA27)
DATA28: U1.G11 (DATA28)
DATA29: U1.G16 (DATA29)
DATA30: U1.H13 (DATA30)
DATA31: U1.F13 (DATA31)
EINT0: U1.N17 (EINT0/GPF0)
EINT1: U1.M16 (EINT1/GPF1)
EINT2: U1.L13 (EINT2/GPF2)
EINT4: U1.M17 (EINT4/GPF4)
EINT7: U1.L16 (EINT7/GPF7)
FRnB: R1.1, U1.G6 (FRnB)
GND: C1.1, C2.1, C3.1, C4.1, C5.1, C6.1, C9.2, C10.2, C11.2, C13.2, C14.2, C15.2, C16.2, C17.2, C18.2, C20.2, C21.2, C23.2, C24.2, R6.2, R44.2, U1.A3 (VSSi), U1.A4 (VSSi), U1.A5 (VSSMOP), U1.A7 (VSSMOP), U1.A11 (VSSMOP), U1.A12 (VSSi), U1.A15 (VSSMOP), U1.B1 (VSSMOP), U1.B10 (VSSi), U1.B13 (VSSMOP), U1.C17 (VSSi), U1.D16 (VSSMOP), U1.D17 (VSSMOP), U1.E2 (VSSMOP), U1.F2 (VSSi), U1.G1 (VSSOP), U1.G17 (VSSi), U1.H1 (VSSiarm), U1.H11 (VSSOP), U1.K1 (VSSiarm), U1.M12 (VSSA_UPLL), U1.N1 (VSSOP), U1.P13 (OM2), U1.P15 (AIN3), U1.P16 (XP/AIN7), U1.R13 (OM1), U1.R14 (AIN0), U1.R15 (AIN2), U1.R16 (XM/AIN6), U1.R17 (VSSA_MPLL), U1.T1 (VSSiarm), U1.T2 (VSSiarm), U1.T13 (OM3), U1.T14 (VSSA_ADC), U1.T16 (YM/AIN4), U1.T17 (YP/AIN5), U1.U3 (VSSOP), U1.U4 (VSSiarm), U1.U7 (VSSiarm), U1.U9 (VSSOP), U1.U10 (VSSiarm), U1.U15 (VSSOP), U1.U17 (AIN1), Y1.2, Y1.4
LCD_DC: U1.R11 (EINT14/SPIMOSI1/GPG6)
LCD_RES: U1.K10 (EINT13/SPIMISO1/GPG5)
LCD_SCL: U1.L9 (SPICLK0/GPE13)
LCD_SDA: U1.P9 (SPIMOSI0/GPE12)
unnamed: C1.2, U1.N14 (MPLLCAP)
unnamed: C6.2, U1.P17 (UPLLCAP)
unnamed: R2.2, U1.D6 (nSCAS)
unnamed: R3.2, U1.C6 (nSRAS)
unnamed: R4.2, U1.E4 (nWAIT)
unnamed: R5.2, U1.H14 (nBATT_FLT)
unnamed: R8.2, U1.B4 (SCLK0)
unnamed: R9.2, U1.B3 (SCLK1)
unnamed: R10.2, U1.A2 (SCKE)
unnamed: R11.2, U1.D2 (nGCS6)
unnamed: R6.1, R39.1, U1.T15 (OM0)
unnamed: R39.2, SW2.2 (B)
unnamed: R40.2, U1.R12 (NCON)
unnamed: R41.2, U1.J12 (PWREN)
unnamed: R42.1, U1.T11 (EINT21/GPG13)
unnamed: R43.1, U1.L11 (EINT22/GPG14)
unnamed: R44.1, U1.U13 (EINT23/GPG15)
RXD0: U1.K14 (RXD0/GPH3)
SCKE: R10.1
SCLK0: R8.1
SCLK1: R9.1
TCK: U1.J13 (TCK)
TDI: U1.H17 (TDI)
TDO: U1.J16 (TDO)
TMS: U1.J14 (TMS)
TOUT0: U1.J6 (TOUT0/GPB0)
TOUT1: U1.J5 (TOUT1/GPB1)
TOUT2: U1.J7 (TOUT2/GPB2)
TOUT3: U1.K3 (TOUT3/GPB3)
TXD0: U1.K13 (TXD0/GPH2)
VDD_1.3V: C10.1, C13.1, C15.1, C17.1, C20.1, C23.1, U1.A1 (VDDi), U1.A6 (VDDi), U1.A10 (VDDi), U1.A16 (VDDi), U1.B11 (VDDi), U1.F1 (VDDi), U1.F16 (VDDi), U1.G4 (VDDalive), U1.J2 (VDDiarm), U1.J17 (VDDalive), U1.L2 (VDDiarm), U1.M13 (VDDA_UPLL), U1.N16 (VDDA_MPLL), U1.T6 (VDDiarm), U1.T8 (VDDiarm), U1.U1 (VDDiarm), U1.U2 (VDDiarm), U1.U11 (VDDi)
XTIpll: C2.2, U1.G14 (XTIpll), Y1.3
XTOpll: C3.2, U1.G15 (XTOpll), Y1.1
Xtirtc: C4.2, U1.M14 (Xtirtc), Y2.2
Xtortc: C5.2, U1.L12 (Xtortc), Y2.1
nBE0: U1.D4 (nBE0)
nBE1: U1.B5 (nBE1)
nBE2: U1.D5 (nBE2)
nBE3: U1.E5 (nBE3)
nFCE: R7.2, U1.F4 (nFCE/GPA22)
nFRE: U1.E1 (nFRE/GPA20)
nFWE: U1.F3 (nFWE/GPA19)
nGCS0: U1.F6 (nGCS0)
nGCS4: U1.D3 (nGCS4/GPA15)
nGCS6: R11.1
nOE: U1.C5 (nOE)
nRESET: U1.H16 (nRESET)
nSCAS: R2.1
nSRAS: R3.1
nTRST: U1.H15 (nTRST)
nWE: U1.E6 (nWE)

Notes on the sheet:
Nand flash write enable
JTAG, Data Input
IIS-bus serial clock
indicates that the current bus cycle is a read cycle
External timer clock input
IIS-bus serial data input
USB Host/Device
PWM/Timer output
IIS-bus serial data output
External clock source for MPLL UPLL, If it isn't used, it has to be High (VDDOP)
core logic VSS
SDRAM column address strobe
I/O port VDD (3.3V)
SD clock
SDRAM
SDRAM clock
Probe for battery state, If it isn't used, it has to be High (VDDOP)
JTAG, Reset
NOR FLASH
CAMERA Interface
ADC input[7:0]. If it isn't used pin, it has to be low (ground) Touch Screen
DM9000A Interrupt Request
UART TXD
memory I/O VDD
reset block and port status register VDD
LCD data bus
1.2V/1.3V core power on-off control signal
ADC VDD(3.3V)
UART Ch 0
core logic VDD for ARM core
Nand flash COMMAND LATCH ENABLE
LCD clock signal
LCD line signal
for specific TFT LCD
JTAG, Mode Select
Nand flash read enable
UART RXD
External clock input for UART
VM alternates the polarity of the row and column voltage
Ethernet
IIS-bus channel select clock
I/O port VSS
SDRAM data mask
Nand flash chip enable
SD receive/transmit data
core logic VDD for Internal block
SOC
RTC VDD (3.0V, Input range: 1.8 ~ 3.6V)
NAND flash memory configuration (Page size)(Address cycle)(Bus width) 2KBytes 5 address cycle 8-bit
NAND flash memory configuration advance (Normal / Advance)
Loop filter capacitor for USB clock
Loop filter capacitor for main clock
TFT: Line end signal
LCD frame signal
For external device reset control
UPLL analog and digital VDD
IIS-Bus CODEC system clock
nWAIT requests to prolong a current bus cycle. As long as nWAIT is L, the current bus cycle cannot be completed
SDRAM clock enable
JTAG, Clock
SD command
JTAG, Data Output
OM[1:0] = 00: Nand-boot 01: 16-bit OM[3:2] = 00b, Crystal is used for MPLL CLK source and UPLL CLK source.
CLOCK OUT
SDRAM row address strobe
ADC Vref
Nand flash ready/busy * If NAND flash controller isn't used, it has to be pull-up. (VDDMOP)
Nand flash ADDRESS LATCH ENABLE
MPLL analog and digital VDD
